medpex/display-case-gc9a01/docs/img/gallery-matrix-angle.jpg

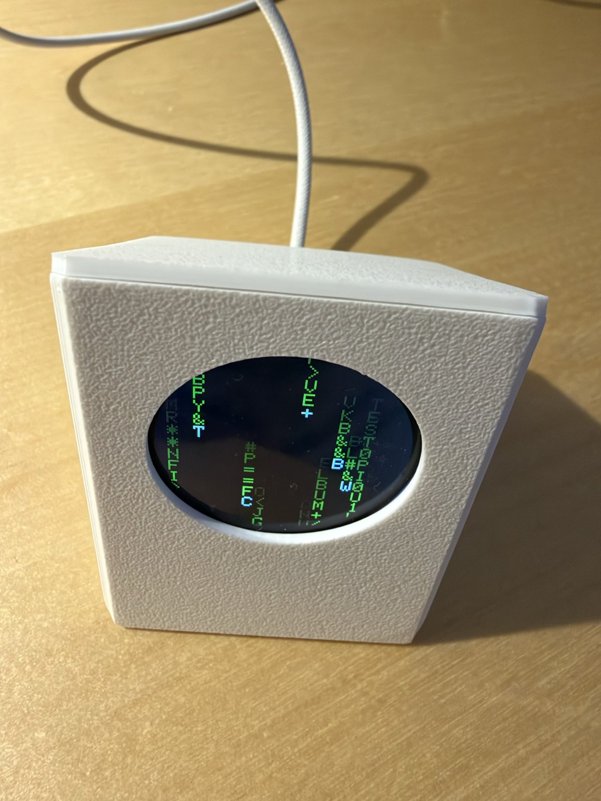
docs/img/gallery-matrix-angle.jpg
