medpex/display-case-gc9a01/docs/img/gallery-sun.jpg

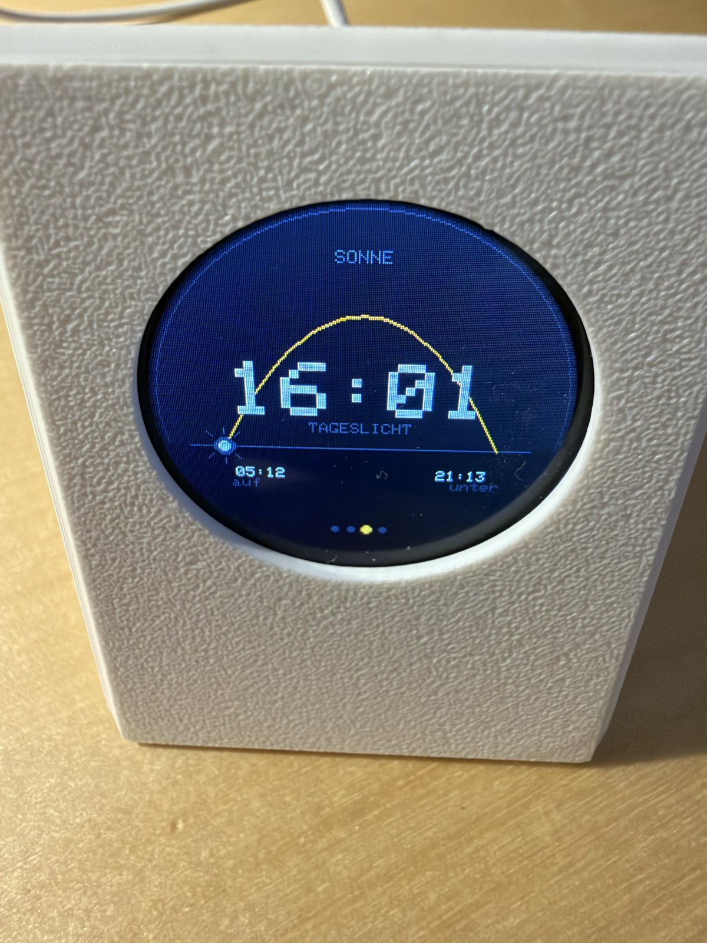
docs/img/gallery-sun.jpg
