medpex/display-case-gc9a01/docs/img/gallery-weather.jpg

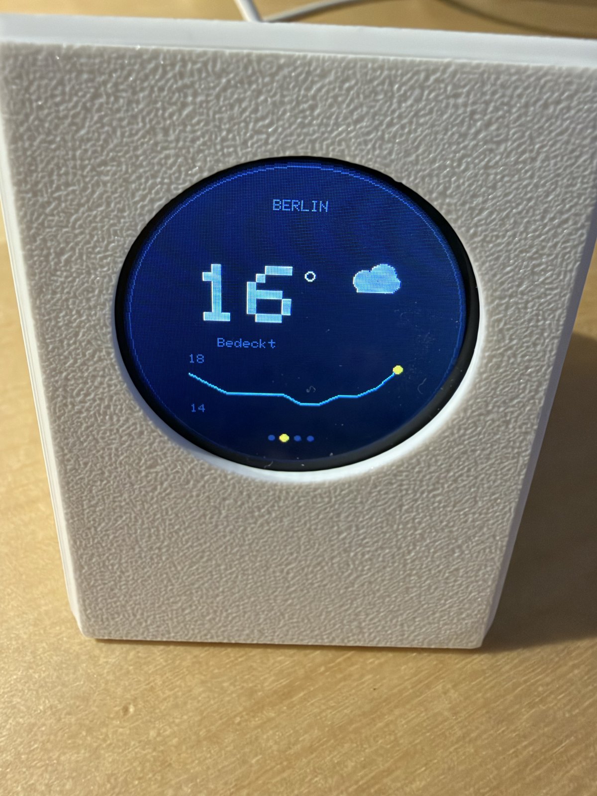
docs/img/gallery-weather.jpg
