medpex/display-case-gc9a01/puck/docs/img/photos/photo-front-low.jpg

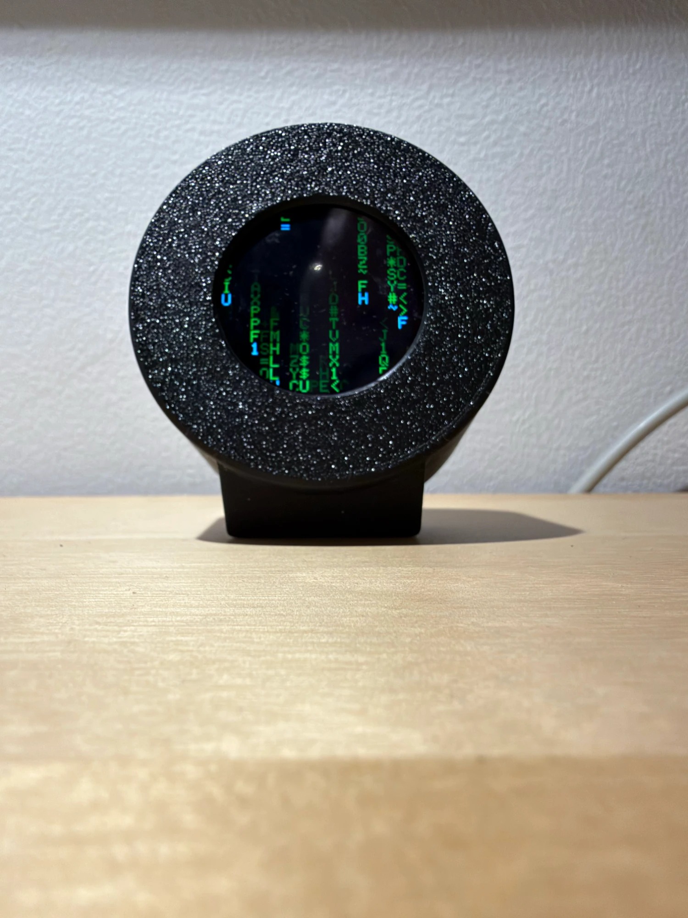
puck/docs/img/photos/photo-front-low.jpg
