medpex/display-case-gc9a01/puck/docs/img/render-rear.png

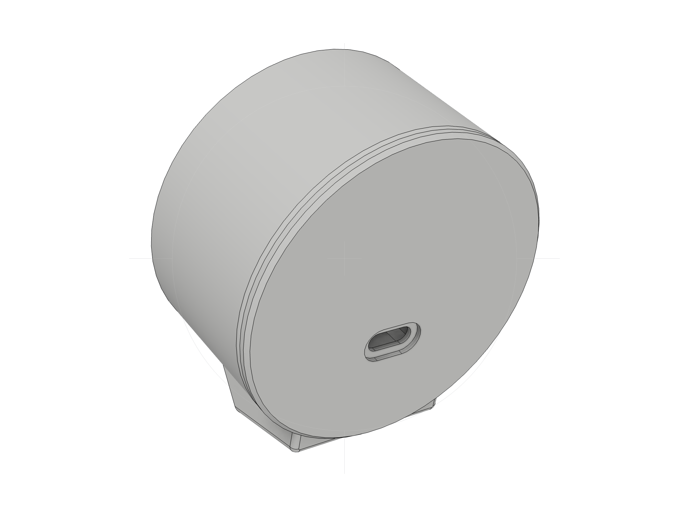
puck/docs/img/render-rear.png
