medpex/display-case-gc9a01/puck/docs/img/render-side.png

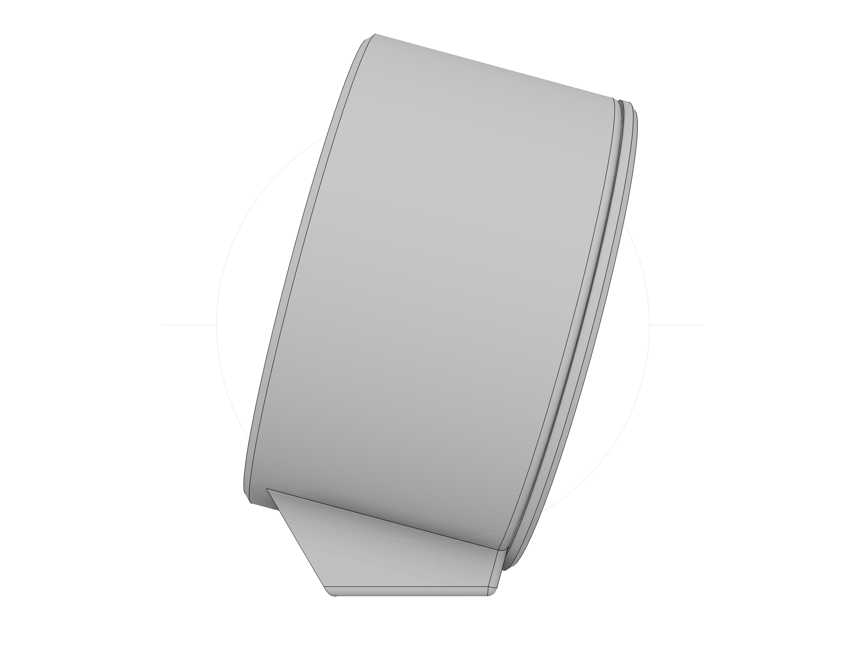
puck/docs/img/render-side.png
