medpex/display-case-gc9a01/docs/img/gallery-wifi-setup.jpg

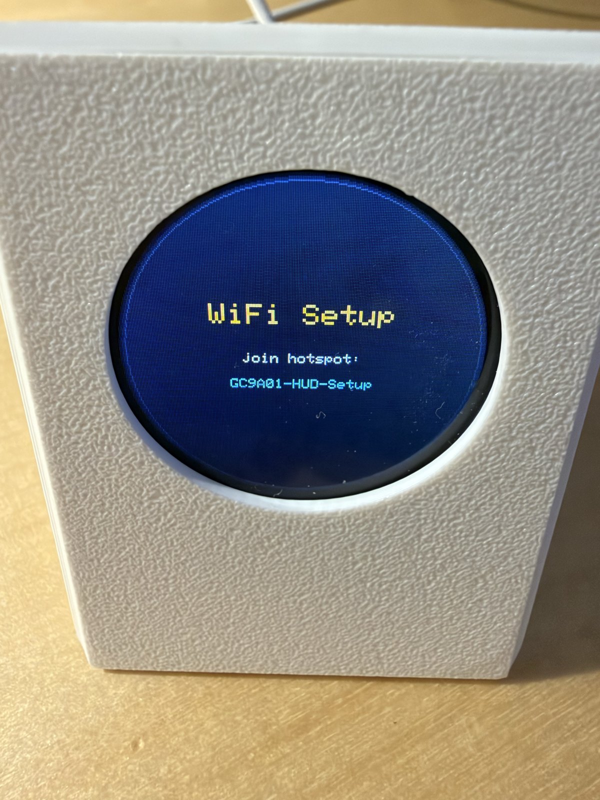
docs/img/gallery-wifi-setup.jpg
